yanava/mhd314/Documentation/Presentations/Live 08.pdf

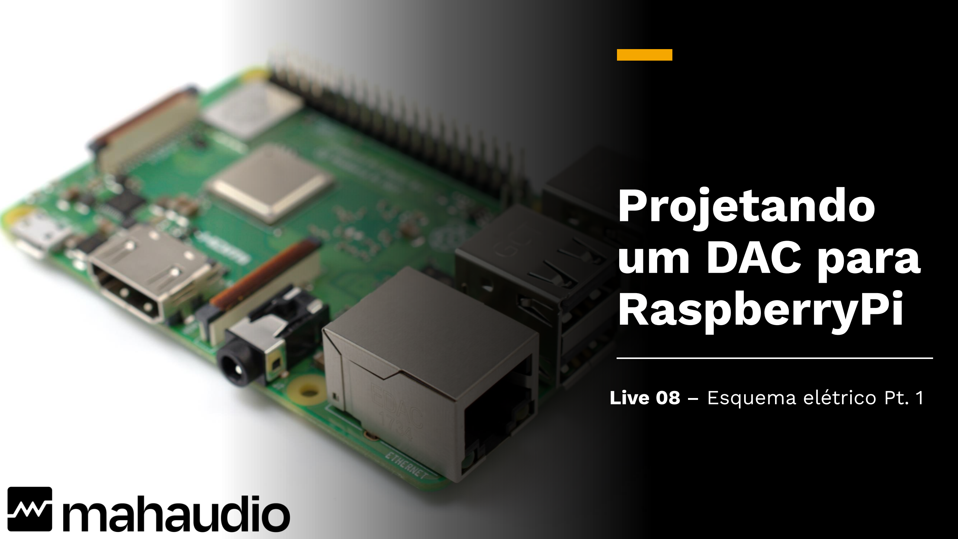
[picture p65: page 1]

# Projetando um DAC para RaspberryPi

## Live 08 – Esquema elétrico Pt. 1

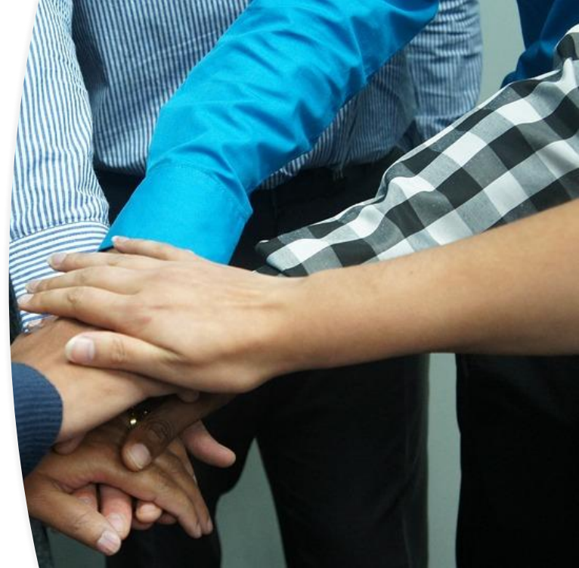
[picture p66: figure]

# Valeu apoiadores!

- Alexandre
- Beatriz
- Cássio
- Digão
- Edson
- Erik
- Henrique
- Leonardo B.
- Leonardo C.
- Luiz
- Rogério

# Resultados

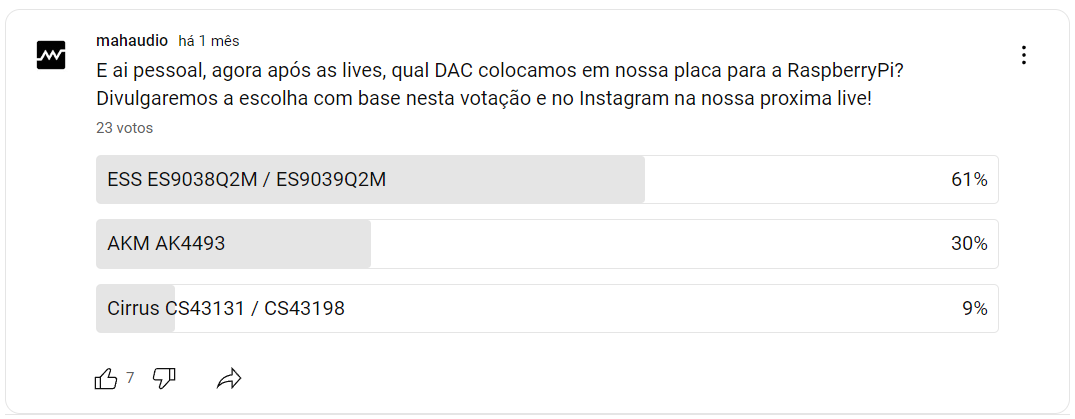
[picture p67: figure]

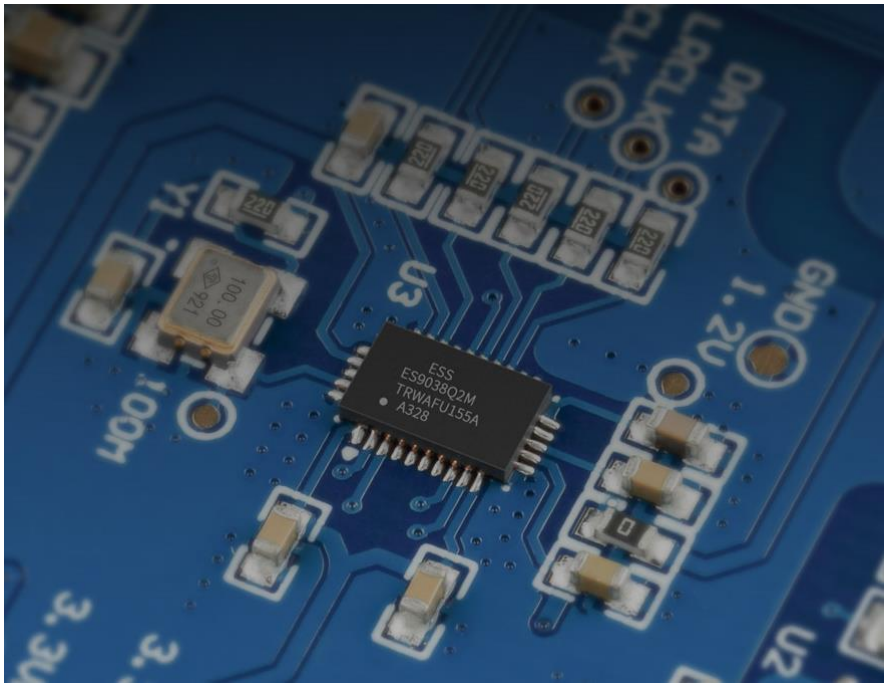
[picture p68: figure]

# Esquema elétrico com ES9038Q2M
