yanava/mhd314/Documentation/Presentations/Live 02.pdf

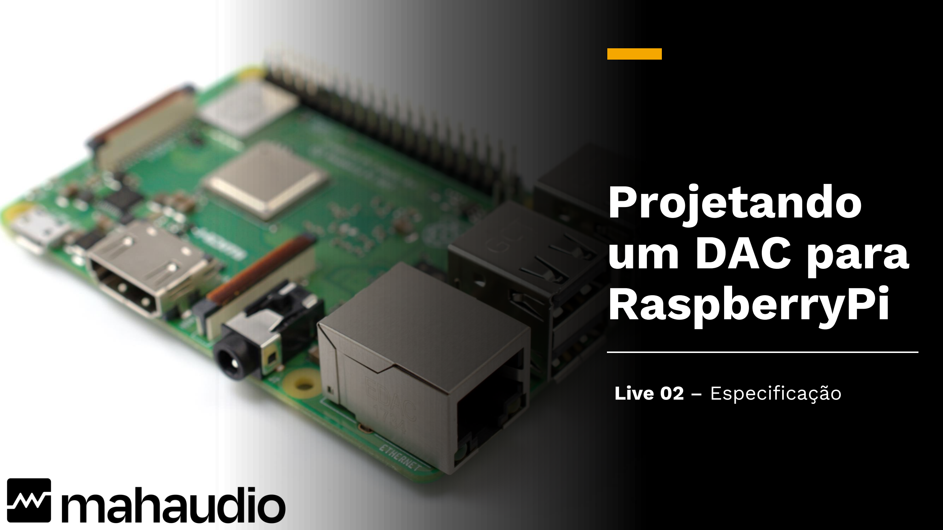
[picture p69: page 1]

# Projetando um DAC para RaspberryPi

## Live 02 – Especificação

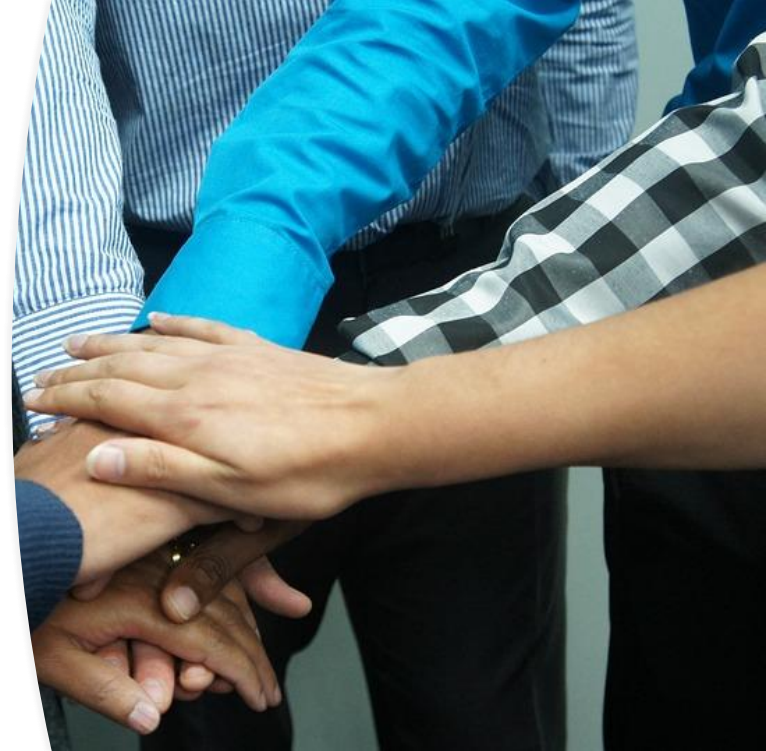
[picture p70: figure]

# Valeu apoiadores!

- Alexandre
- Beatriz
- Cássio
- Digão
- Edson
- Henrique
- Leonardo B.
- Leonardo C.
- Rogério

# Na live anterior

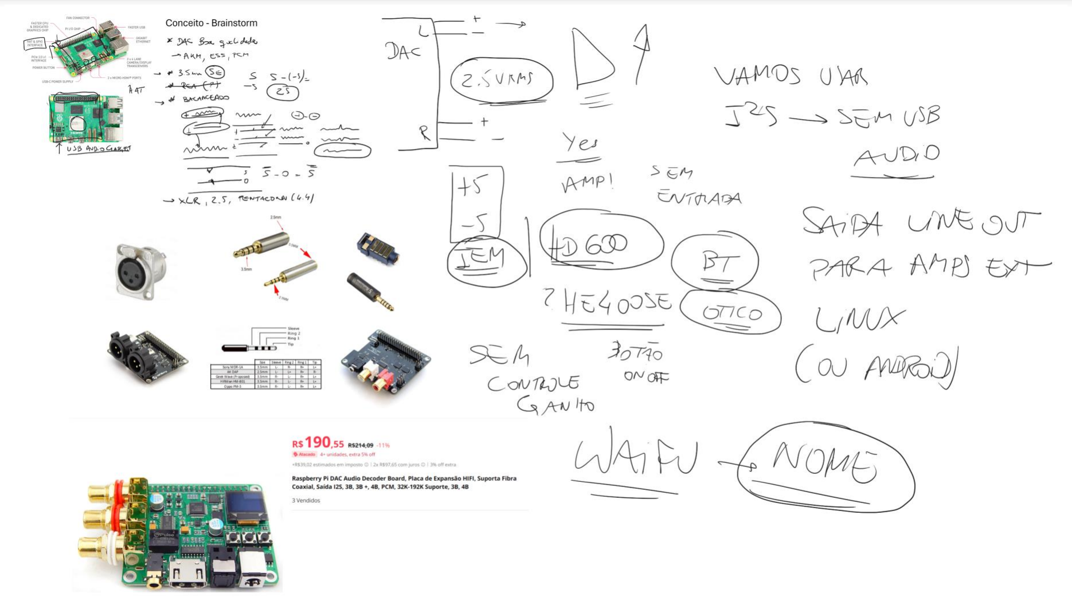
[picture p71: figure]

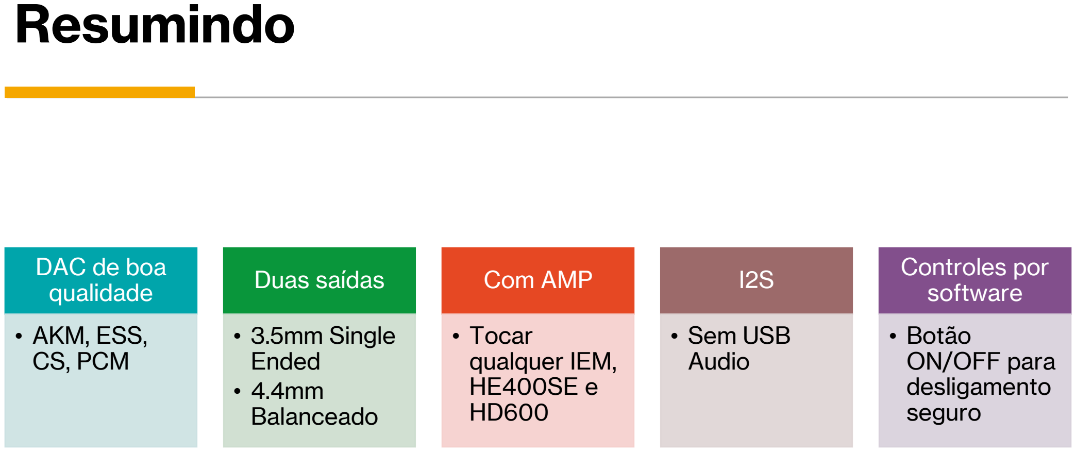
[picture p72: figure]
Resumindo; DAC de boa qualidade; • AKM, ESS, CS, PCM; Duas saídas; • 3.5mm Single Ended • 4.4mm Balanceado; Com AMP; • Tocar qualquer IEM, HE400SE e HD600; • Sem USB Audio; Controles por software; • Botão ON/OFF para desligamento seguro
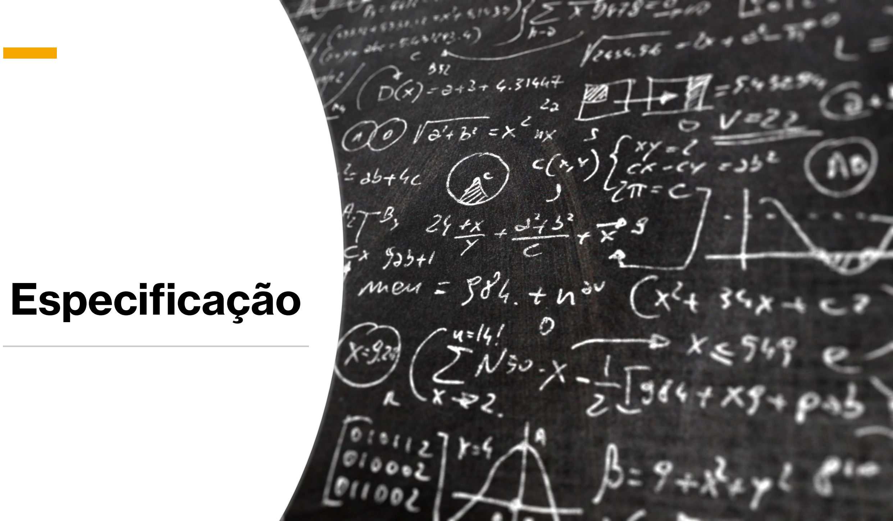
[picture p73: page 5]

# Especificação

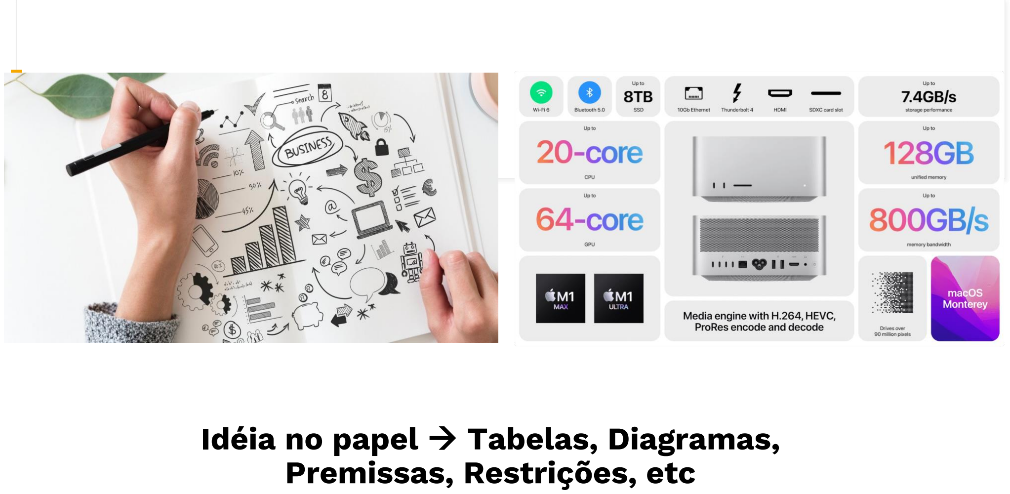
[picture p74: page 6]

Idéia no papel → Tabelas, Diagramas,

# Premissas, Restrições, etc

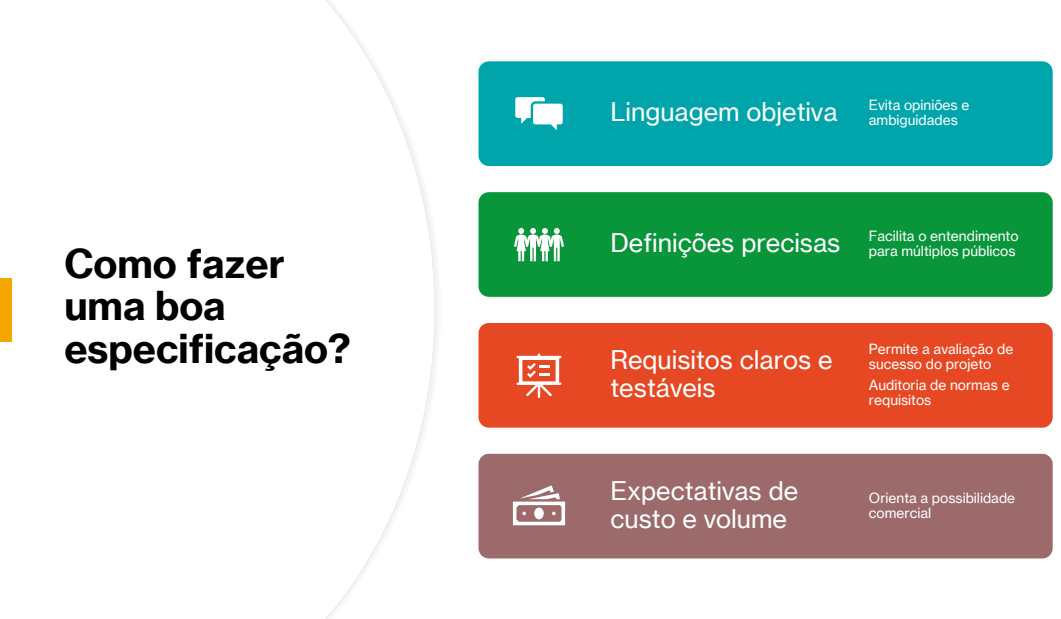
[picture p75: page 7]
Como fazer uma boa especificação?; Linguagem objetiva; Evita opiniões e; ambiguidades; Requisitos claros e testáveis; Expectativas de custo e volume; Orienta a possibilidade comercial

Definições precisas Facilita o entendimento

para múltiplos públicos

Permite a avaliação de
sucesso do projeto
Auditoria de normas e
requisitos

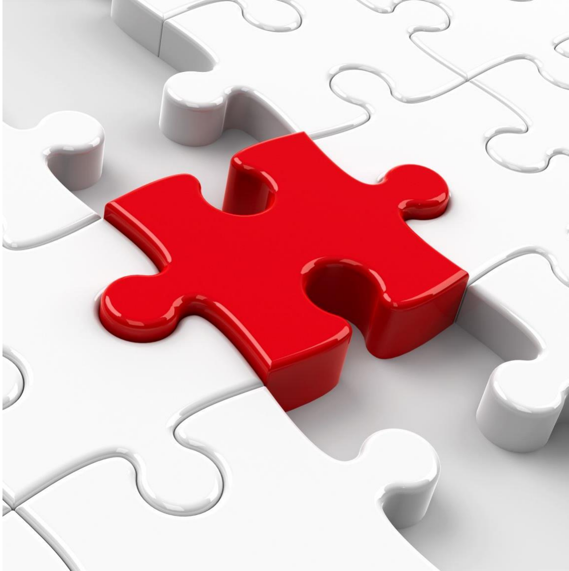
[picture p76: figure]

# Desafios

- Falta de informações
- Falta de conhecimento
- Dependência da escolha de componentes
- Sucesso (Volume) → desconhecido

# Modelo

Item | Descrição | Requisito | Prioridade | Justificativa
1 | Potência de Saída | 100mW SE / 200mW DIFF | Obrigatório | Fones exigentes
2 | Tamanho | 100 x 100 mm | Opcional | Caber no gabinete
3 | ... | ... | ... | ...

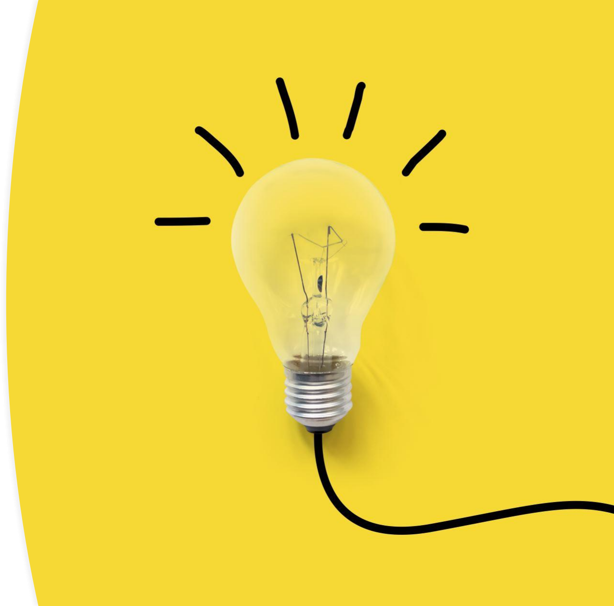
[picture p77: figure]

# Perguntas importantes

- Qual o tamanho físico?
- Quais são as entradas e seus requisitos?
- Quais são as saídas e seus requisitos?
- Quais são os requisitos de energia?
- Há normas a serem atendidas?
- Quais são os blocos do Sistema?
- Custo esperado?

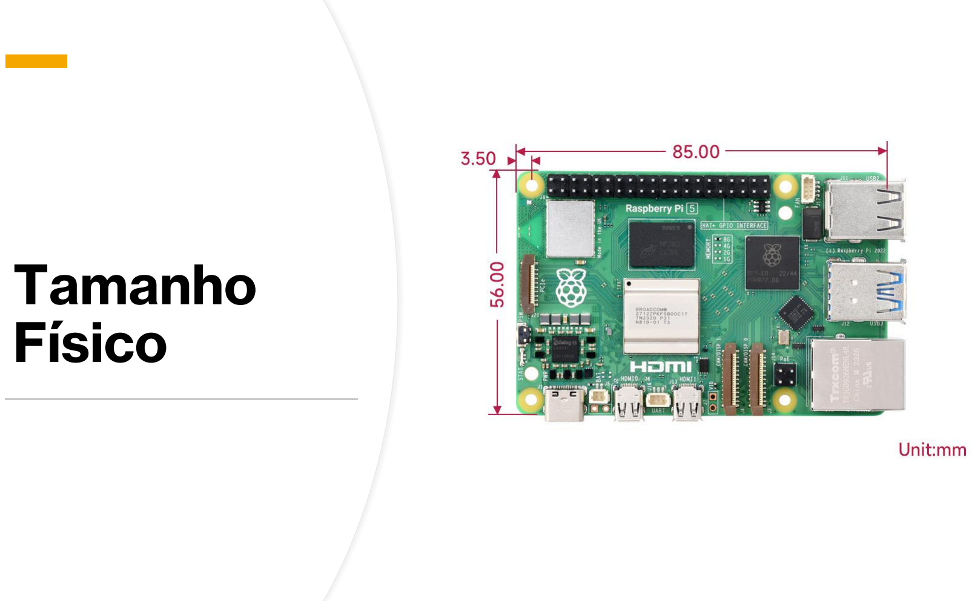
[picture p78: page 11]

# Tamanho Físico

# Alguns formatos em existência

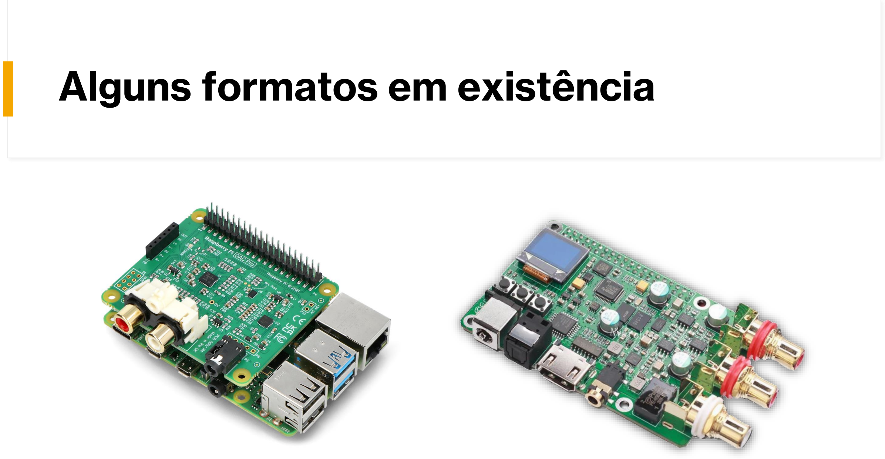
[picture p79: page 12]

# Padronização

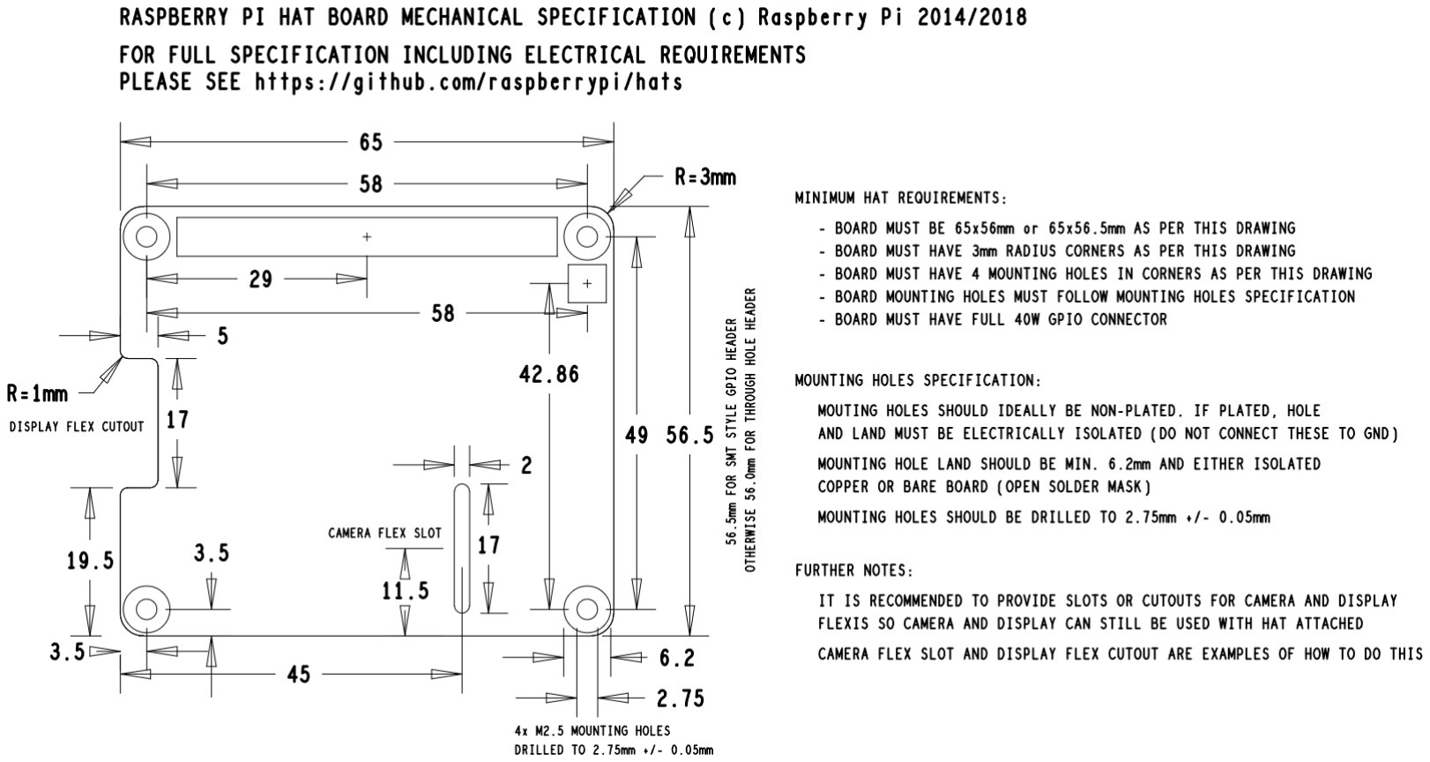
[picture p80: figure]
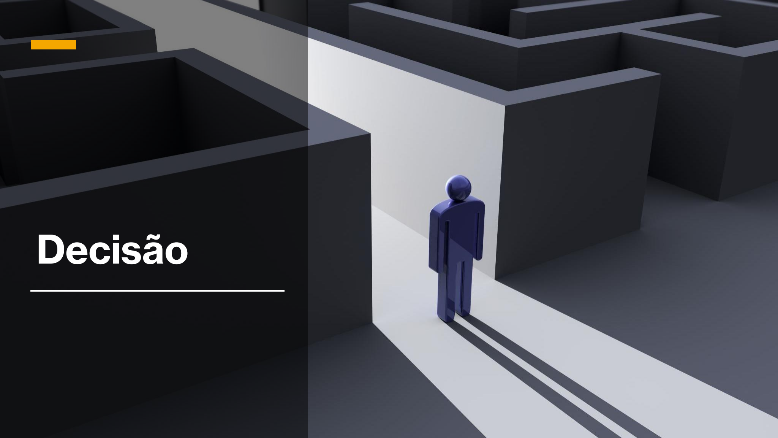
[picture p81: page 14]

# Decisão

# Entradas

## - Entrada de áudio → I2S

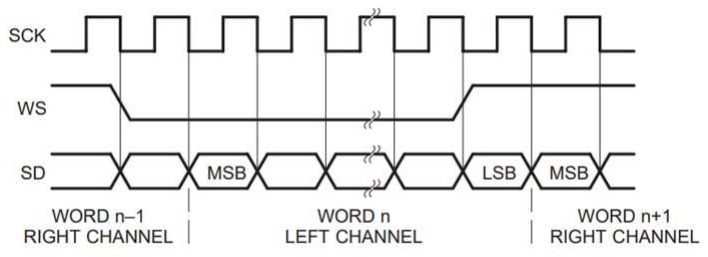
[picture p82: figure]
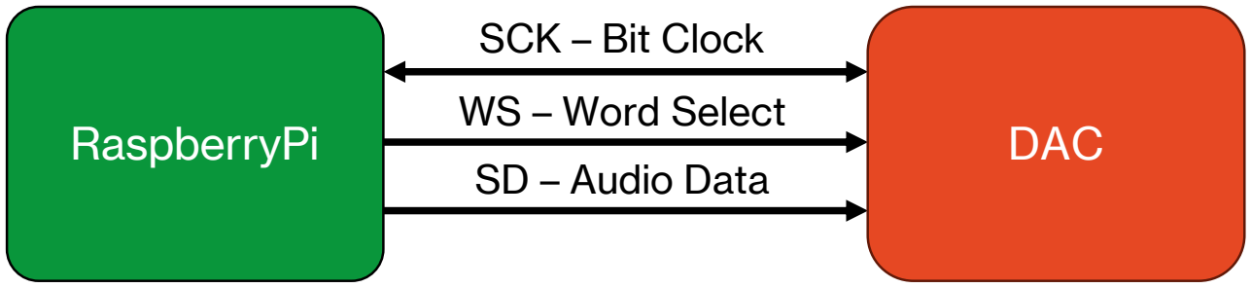
[picture p83: figure]
RaspberryPi; DAC; SD – Audio Data; SCK – Bit Clock; WS – Word Select

# Conector de expansão

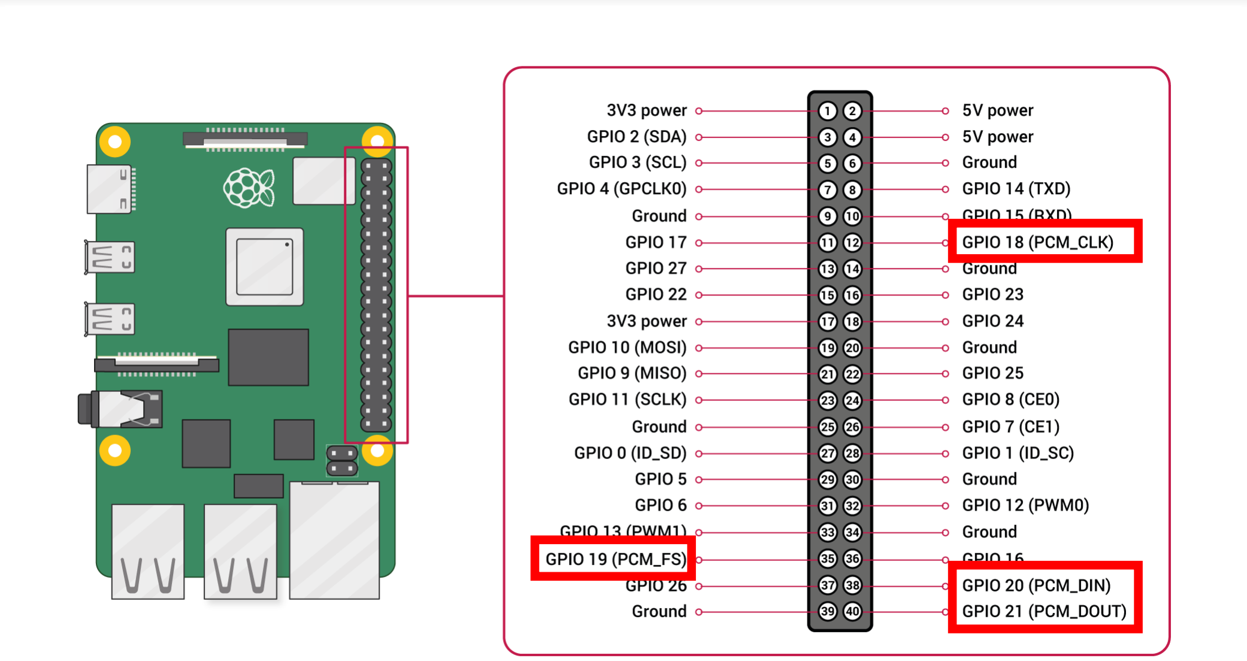
[picture p84: figure]

# Entradas

## - Entrada de configuração → Colocar o DAC no modo correto

- Depende do DAC → I2C, SPI ou similar
- Podemos deixar essa decisão para mais tarde?

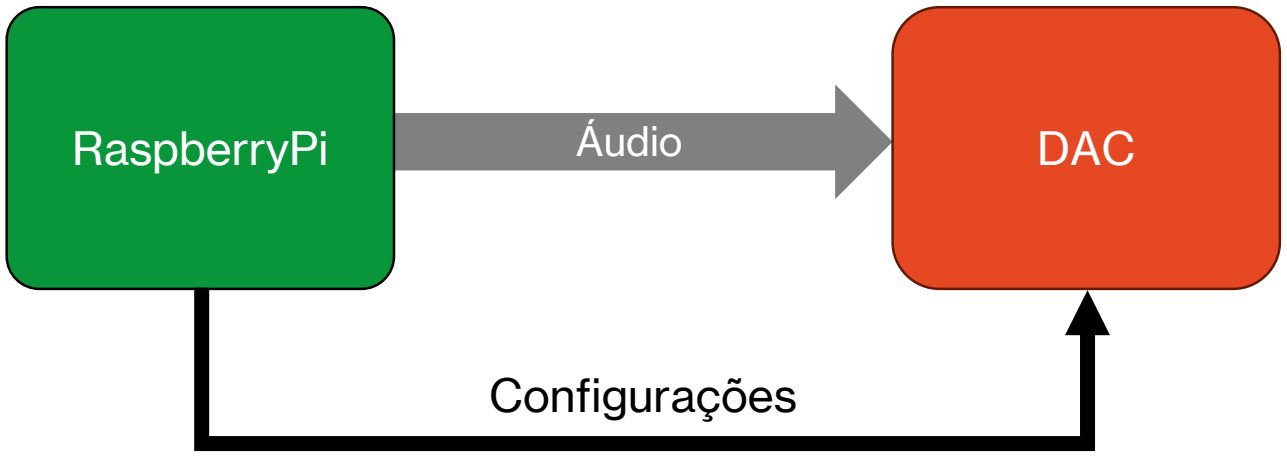
[picture p85: figure]
RaspberryPi; Áudio; DAC; Configurações

# Saídas

## - Já fizemos boa parte do trabalho no conceito inicial!

- Single Ended – 3.5mm
- Diferencial -4.4mm (Pentaconn)

## - Fones “guia”

- Qualquer IEM de referência → Qual?
- HD600
- HE400SE

## - Mas o que isto significa em termos de potência?

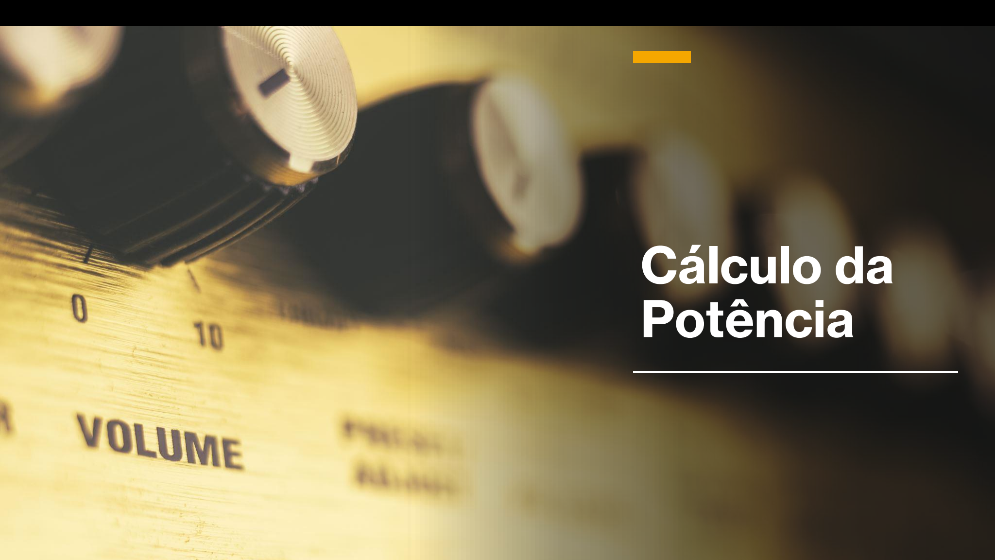
[picture p86: page 19]

# Cálculo da Potência

# Potência – Eletricidade vs Som

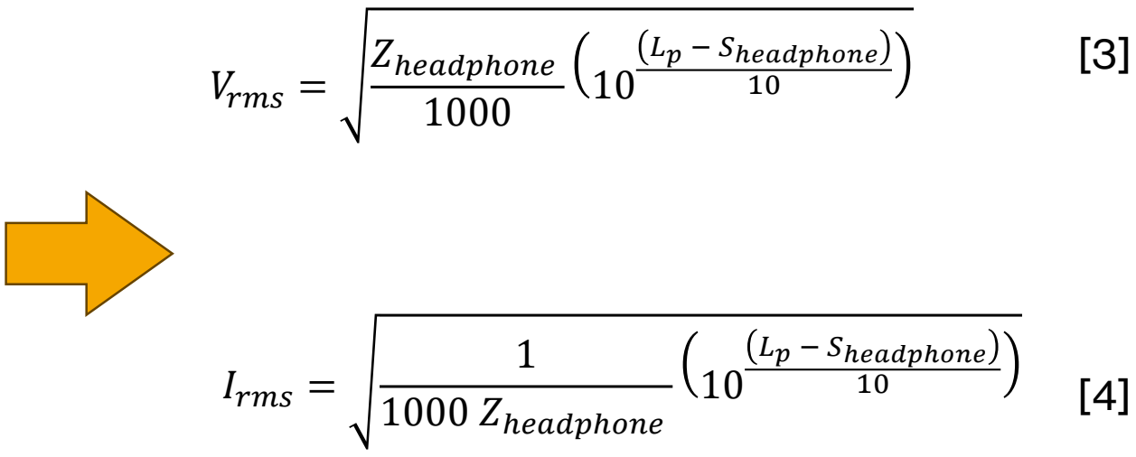
[picture p87: figure]
Vrms =; Zℎeadpℎone; Lp − Sℎeadpℎone 10; Irms =; 1000 Zℎeadpℎone; Lp − Sℎeadpℎone

P W =

Vrms

2

Zℎeadpℎone

= Zℎeadpℎone Irms

2

P(mW) = 10

Lp − Sℎeadpℎone
10

[1]

[2]

# Processo para especificar

## - Conhecer Sensibilidade (S) e Impedância (Z) para um fone alvo

## - Escolher nível de pressão sonora (Lp) adequado

## - Calcular potência (PRMS) e/ou tensão (VRMS) de saída

# Discussão – Pressão Sonora

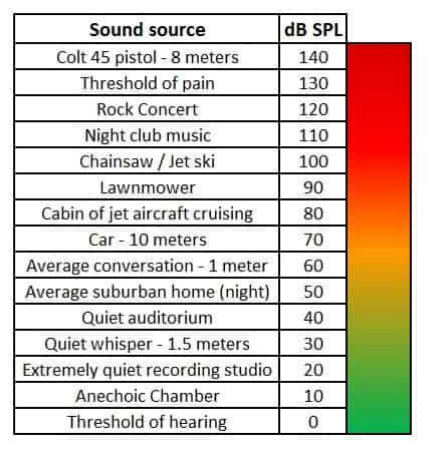
[picture p88: figure]

# Discussão – Nível de pressão sonora

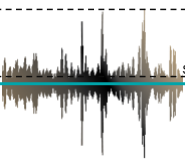
[picture p89: figure]

Som mais forte

Som mais fraco

Faixa dinâmica

Intensidade
Sonora

# Discussão – Nível de pressão sonora

Nivel operacional

Som mais forte

Som mais fraco
Piso de ruído

Limiar de Distorção

Relação sinal ruído
(SNR)

Headroom

Faixa dinâmica

# Nível operacional

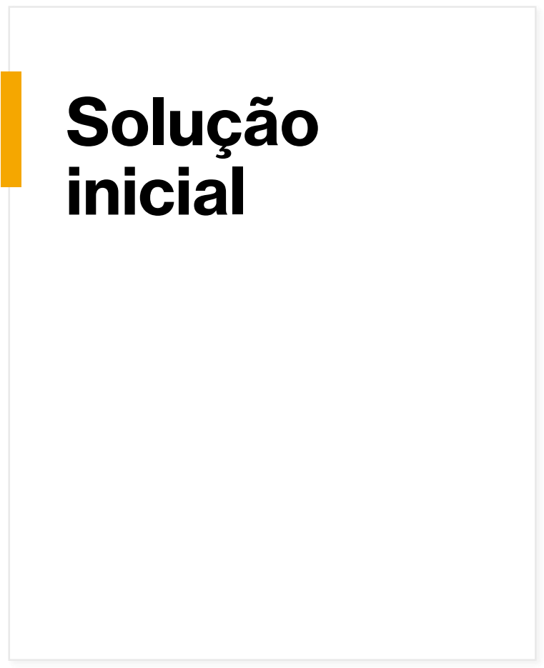
[picture p90: figure]
Solução inicial

# 90dBSPL

# Headroom 20dBSPL

# Pressão Sonora Max 110dBSPL

# Para os fones que decidimos

| Sennheiser HD600 | Hifiman HE400SE
Z | 322Ω | 25.3Ω
Lp | 110dBSPL
S | 100.5dB/mW | 88.7dB/mW
P | 8.91mW | 134.90mW
VRMS | 1.69V | 1.84V
IRMS | 5.27mA | 73.32mA

Fonte:
https://reference-audio-analyzer.pro/en/report/hp/sennheiser-hd-600.phphttps://reference-audio-analyzer.pro/en/report/hp/hifiman-he400se-v2.php

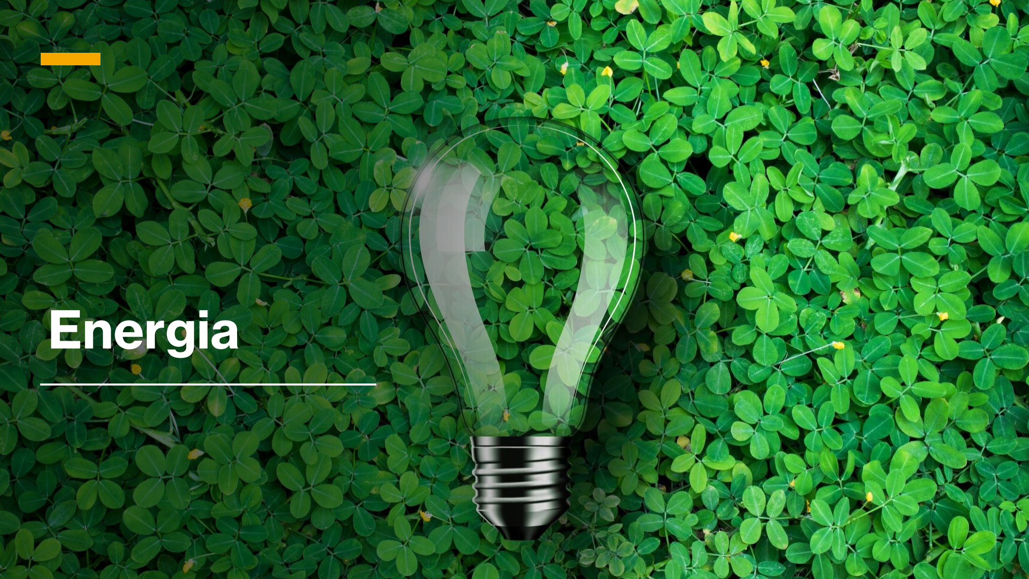
[picture p91: page 27]

# Energia

# Entrada de energia

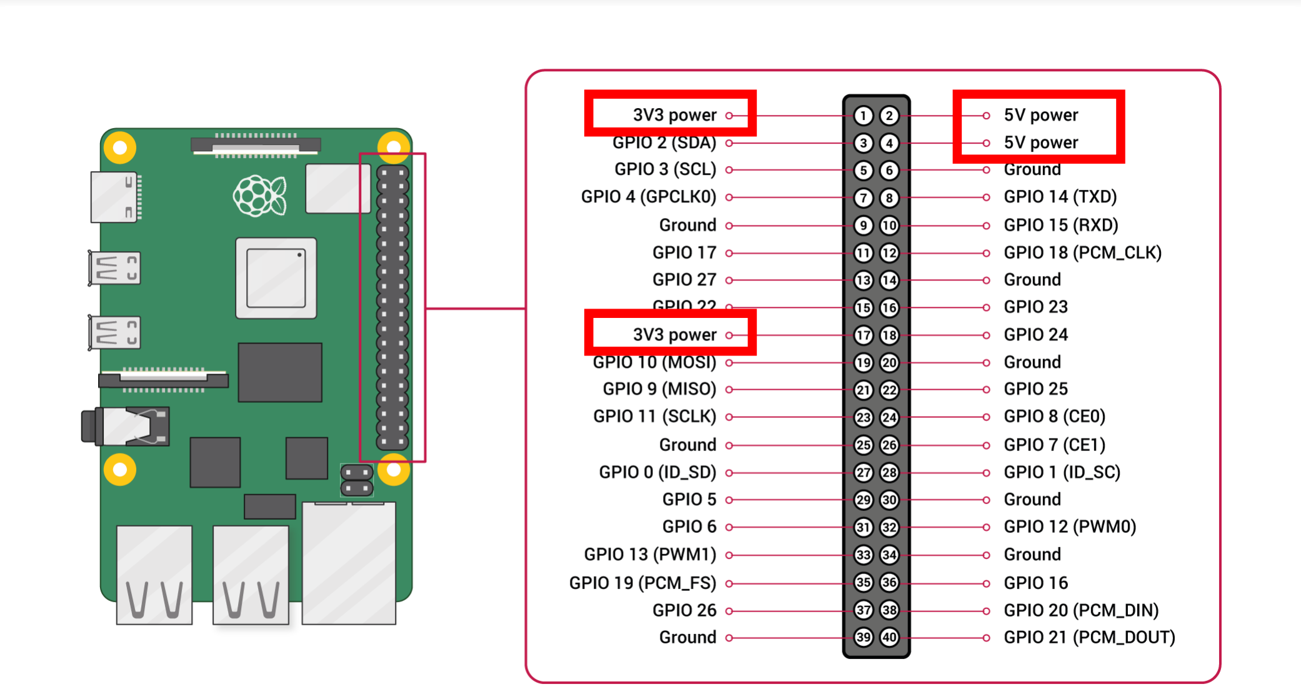
[picture p92: figure]

# Entrada de Energia

## - Duas tensões de entrada

- 5V – Tudo que tem a ver com o DAC
- 3.3V – Tensão de níveis lógicos

## - Potência necessária → Vai depender dos componentes

- Não ultrapassar um máximo pode ser um bom guia
- 5V – 500mA (2.5W)
- 3.3V – 500mA (1.65W)

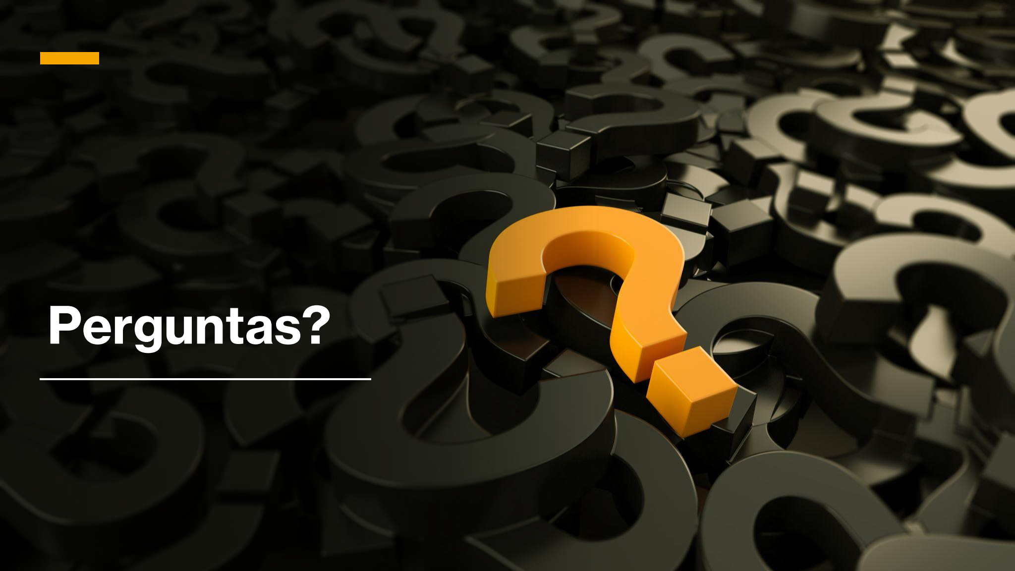
[picture p93: page 30]

# Perguntas?

# Próxima Live

## - Partimos da tabela de spec

## - Vamos desenhar o diagrama de blocos!
