yanava/mhd314/Documentation/Presentations/Live 04.pdf

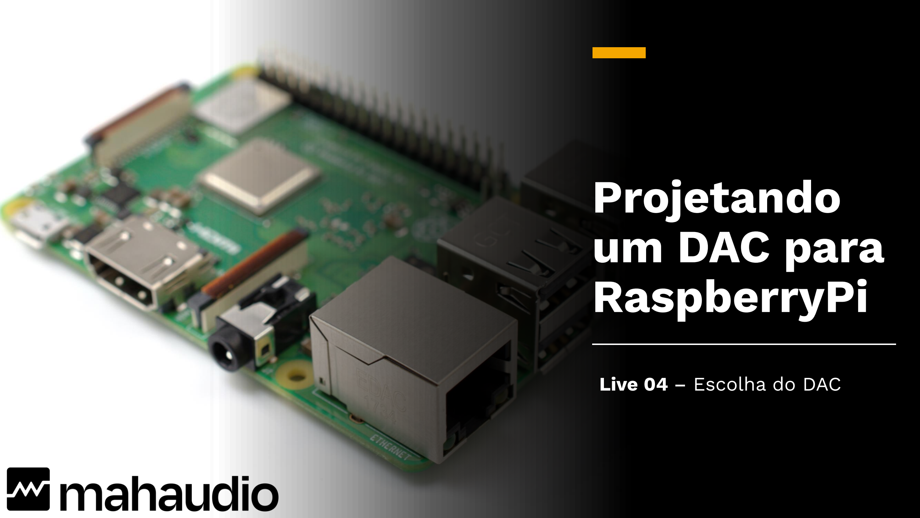
[picture p99: page 1]

# Projetando um DAC para RaspberryPi

Live 04 – Escolha do DAC


## Valeu apoiadores!

- Alexandre
- Beatriz
- Cássio
- Digão
- Edson
- Henrique
- Leonardo B.
- Leonardo C.
- Rogério

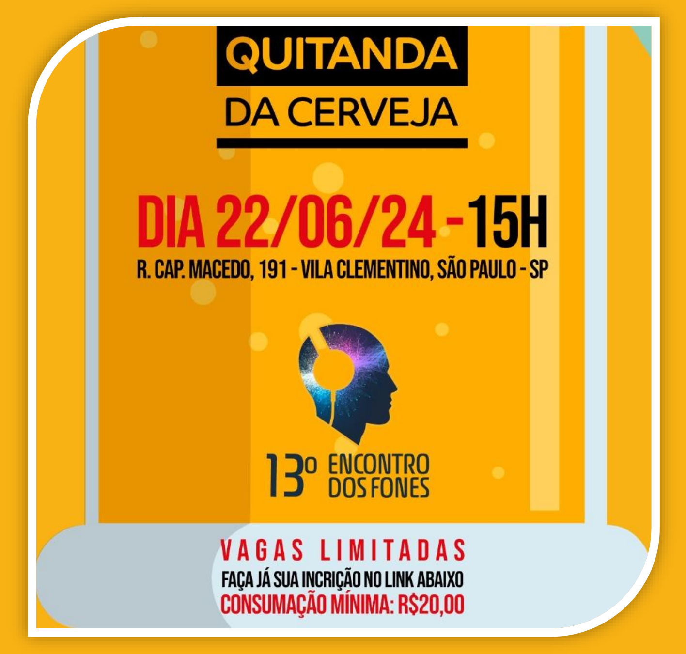
[picture p100: figure]

# Na live anterior

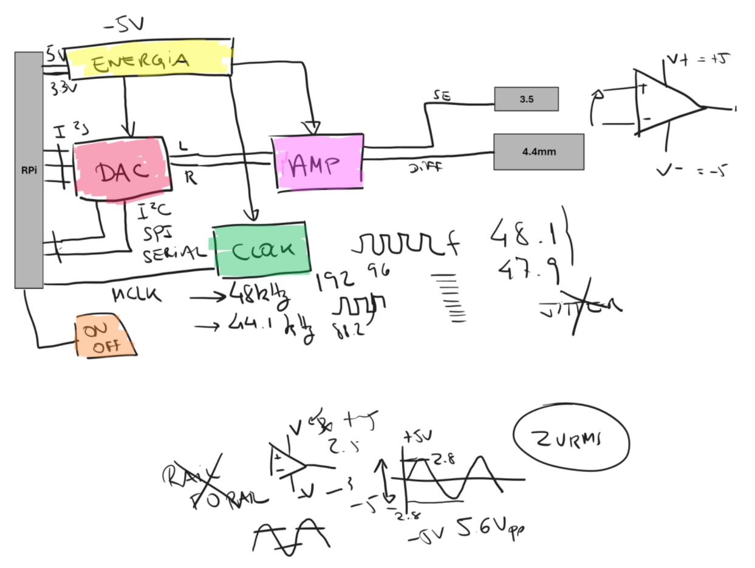
[picture p101: figure]

## Resumindo

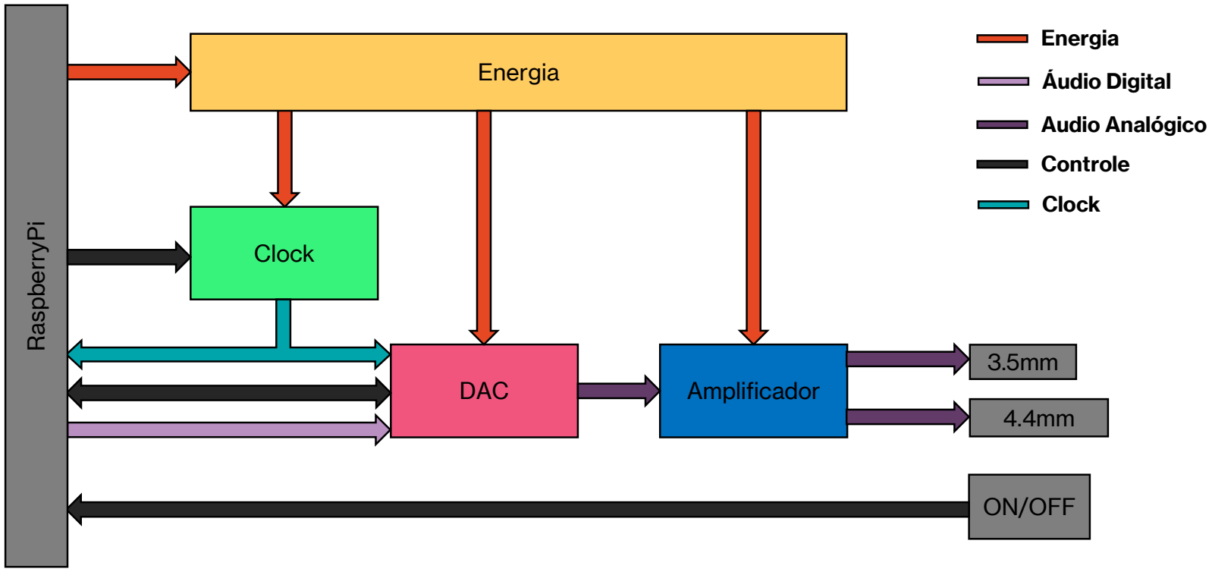
[picture p102: figure]
Energia; DAC; Amplificador; Clock; ON/OFF; RaspberryPi; Audio Analógico; Controle; Áudio Digital
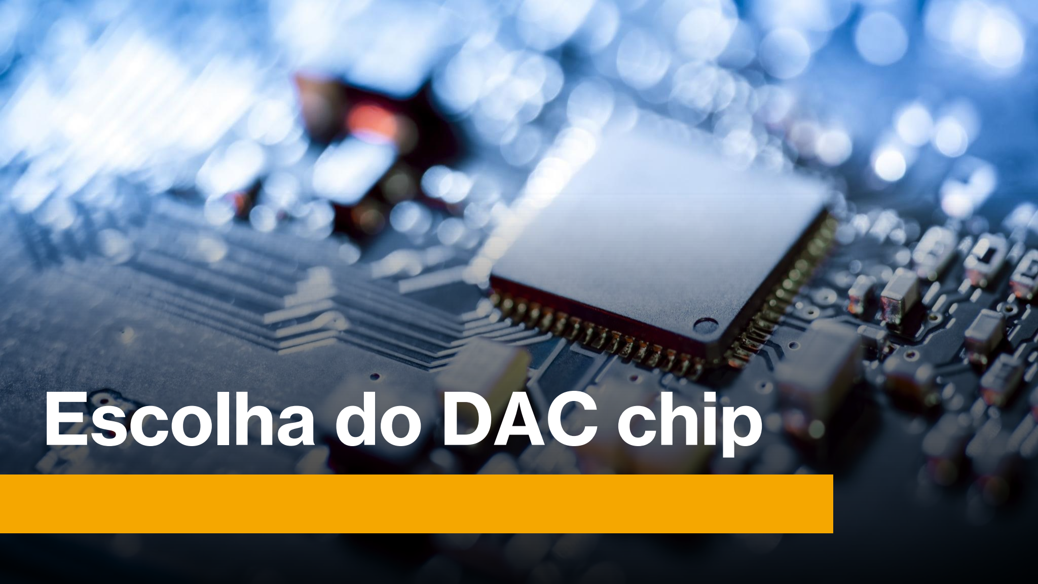
[picture p103: page 6]

# Escolha do DAC chip

## Função de um DAC

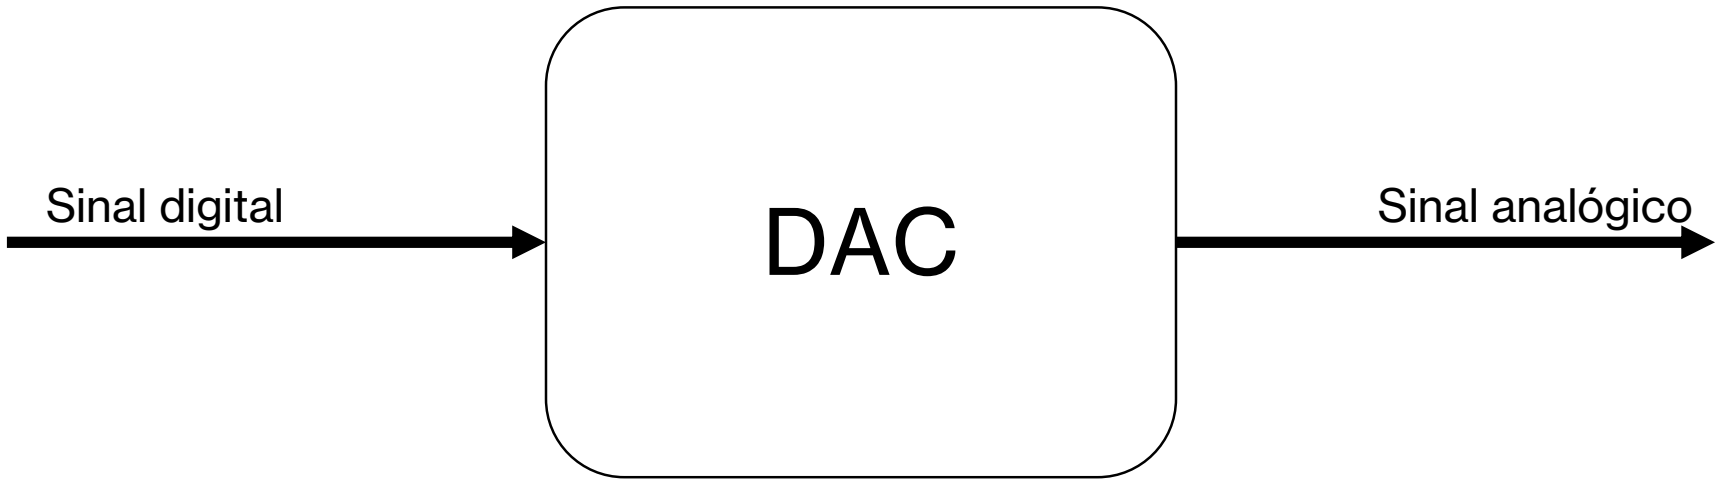
[picture p104: figure]
DAC Sinal digital; Sinal analógico

## Tipos de DAC

- Resistivo
- Escada R-2R
- Delta-Sigma

## Resistivo

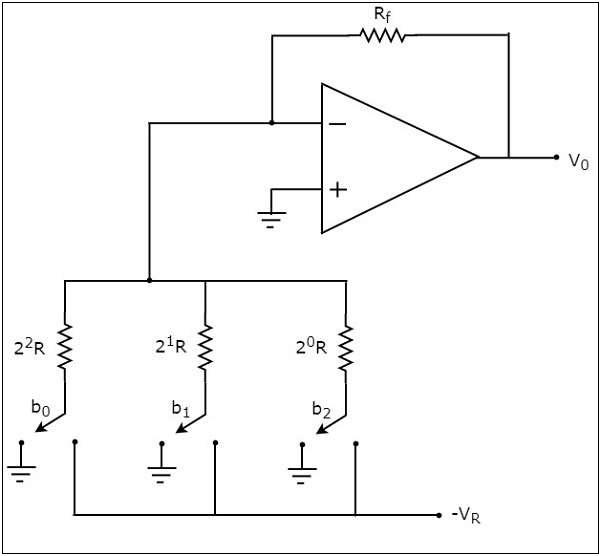
[picture p105: figure]

R-2R

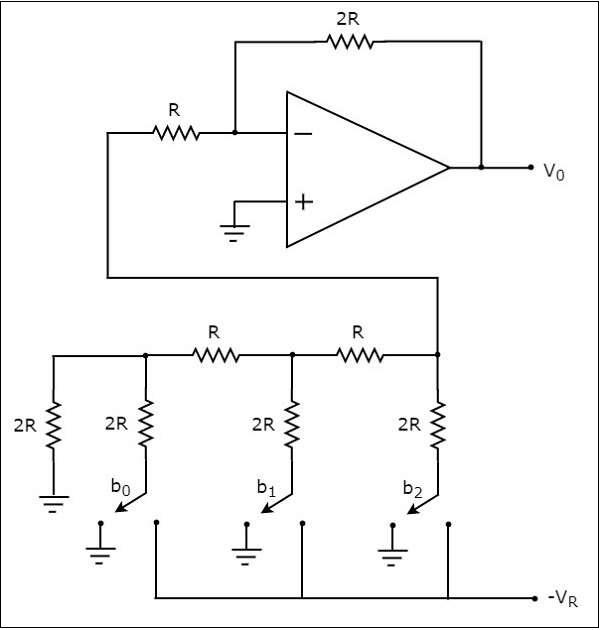
[picture p106: figure]

## Delta-Sigma

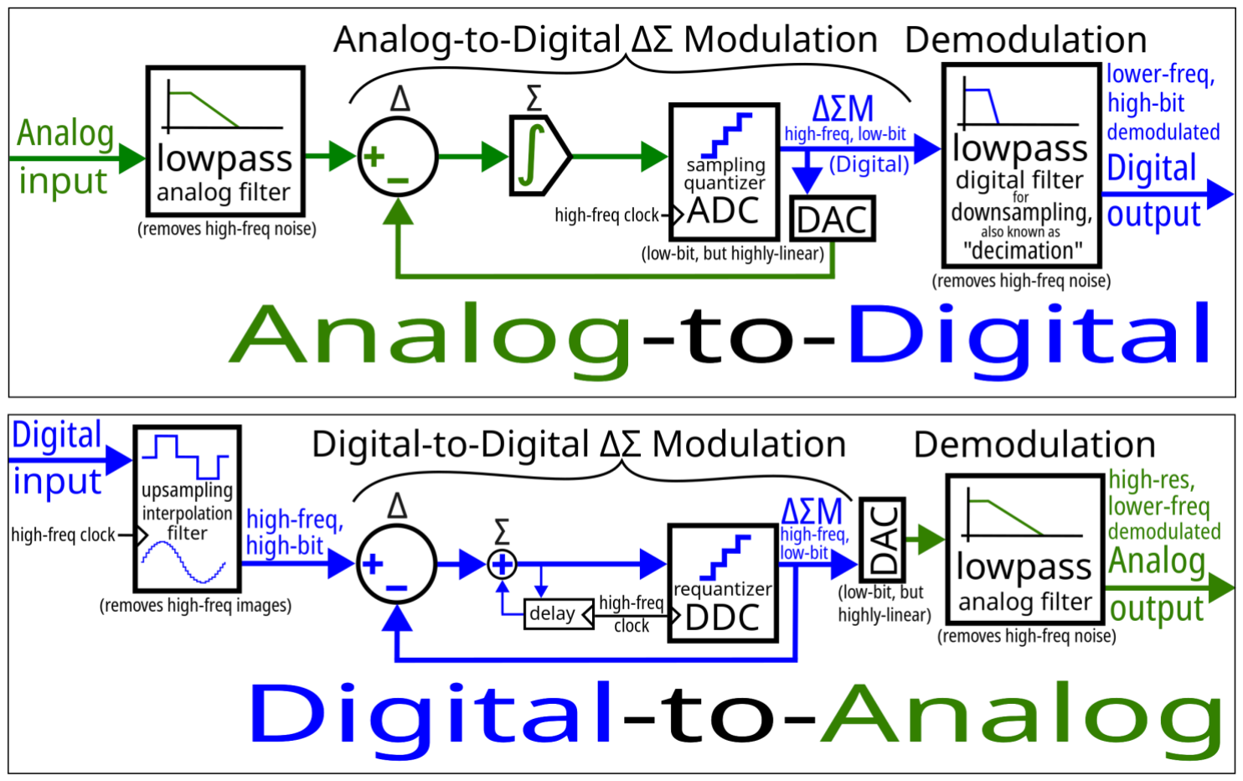
[picture p107: figure]

## Por que Delta-Sigma?

- Popular no mercado
- Alta linearidade → Baixa distorção
- Sobreamostragem → Baixo ruído
- Filtros externos facilmente implementados

Podemos falar mais sobre numa próxima live!

## Alguns pontos esquecidos

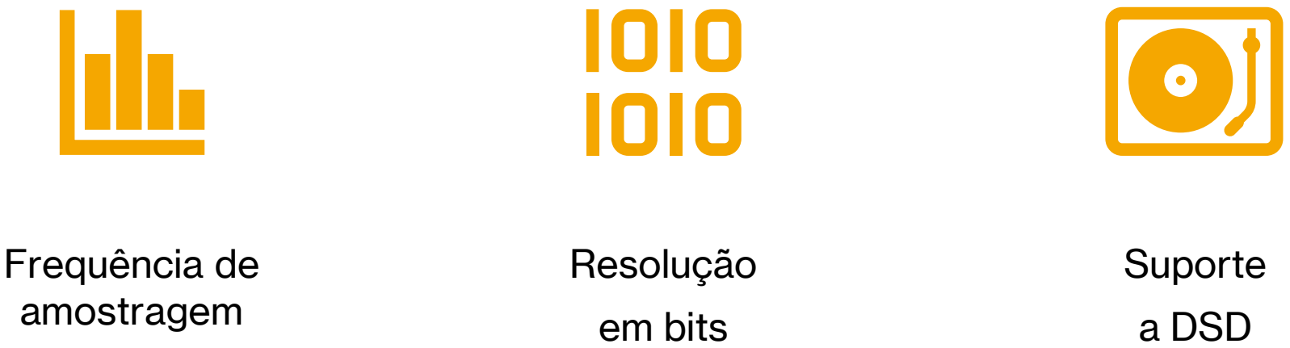
[picture p108: figure]
Frequência de amostragem; Resolução; em bits; Suporte; a DSD

## Outras características técnicas importantes

- SNR
- THD+N
- Faixa dinâmica
- Tipo da saída (diferencial / single-ended)
- Consumo de energia
- Tamanho / Encapsulamento

## Características não técnicas

- Preço unitário
- Disponibilidade
- Data de lançamento
- Popularidade
- Reputação do fabricante

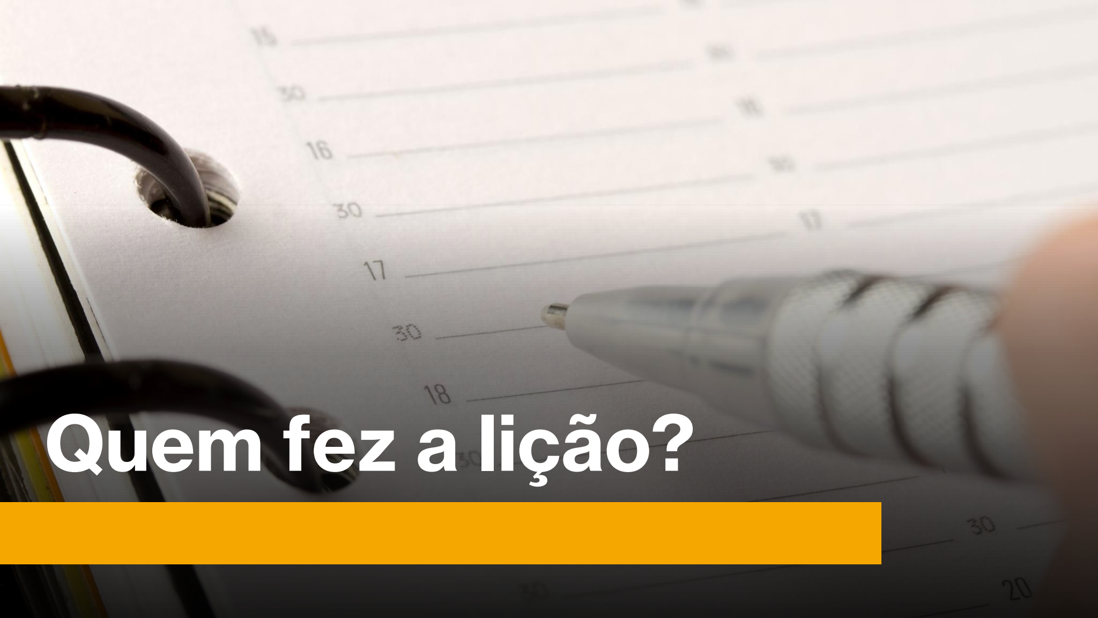
[picture p109: page 16]

# Quem fez a lição?

## Marcas candidatas

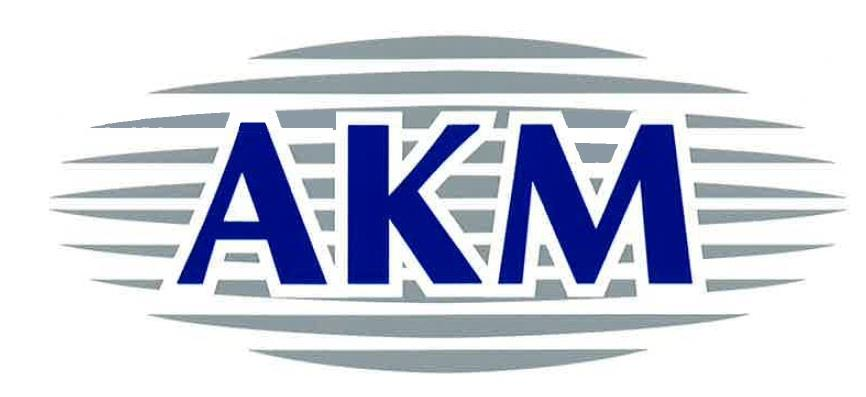
[picture p110: figure]
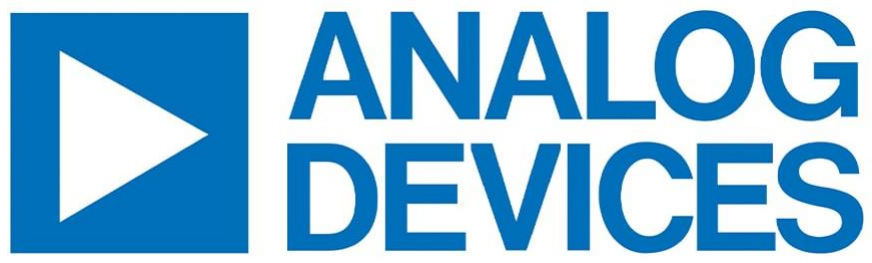
[picture p111: figure]
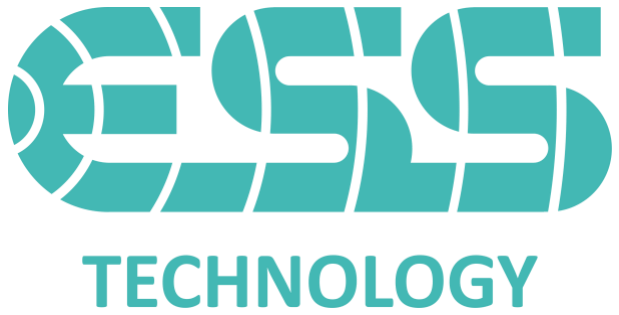
[picture p112: figure]
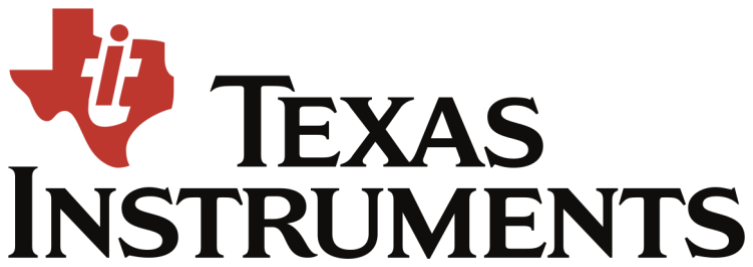
[picture p113: figure]
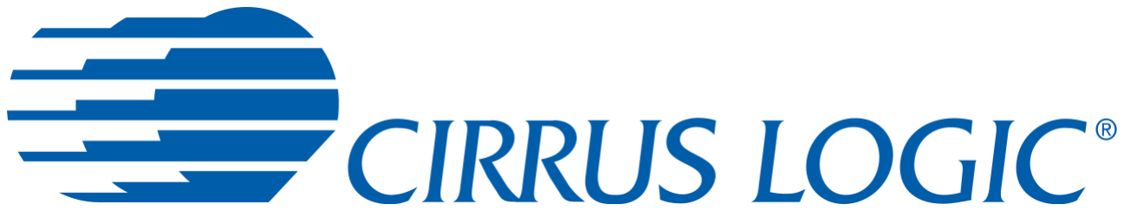
[picture p114: figure]
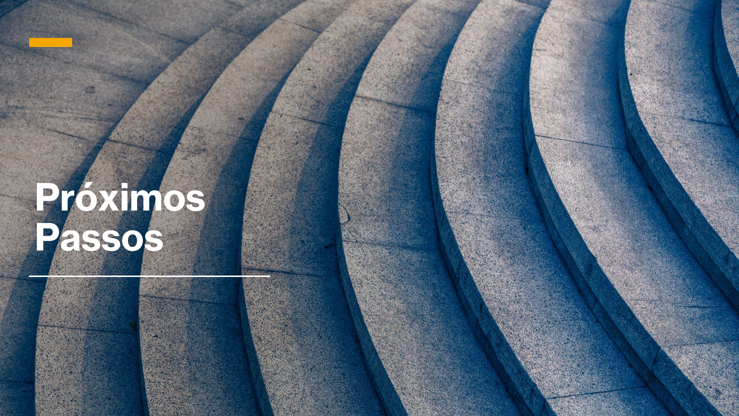
[picture p115: page 18]

# Próximos Passos
