yanava/mhd314/Documentation/Presentations/Live 05.pdf

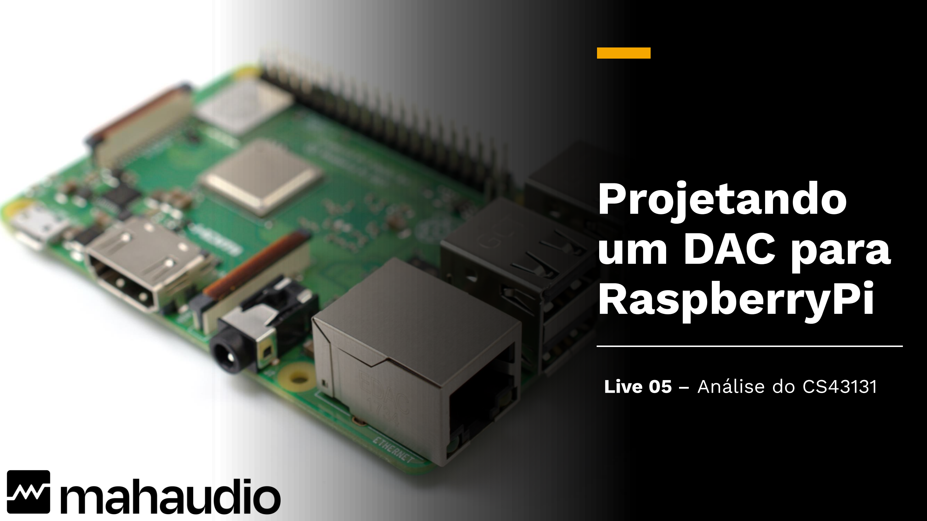
[picture p125: page 1]

# Projetando um DAC para RaspberryPi

## Live 05 – Análise do CS43131


# Valeu apoiadores!

- Alexandre
- Beatriz
- Cássio
- Digão
- Edson
- Erik
- Henrique
- Leonardo B.
- Leonardo C.
- Rogério

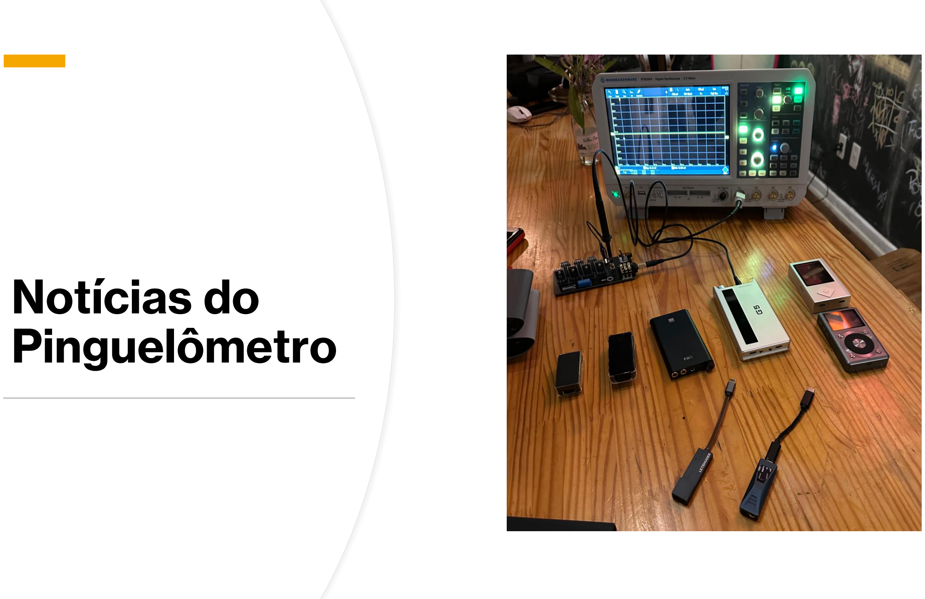
[picture p126: page 3]

# Notícias do Pinguelômetro

# Na live anterior

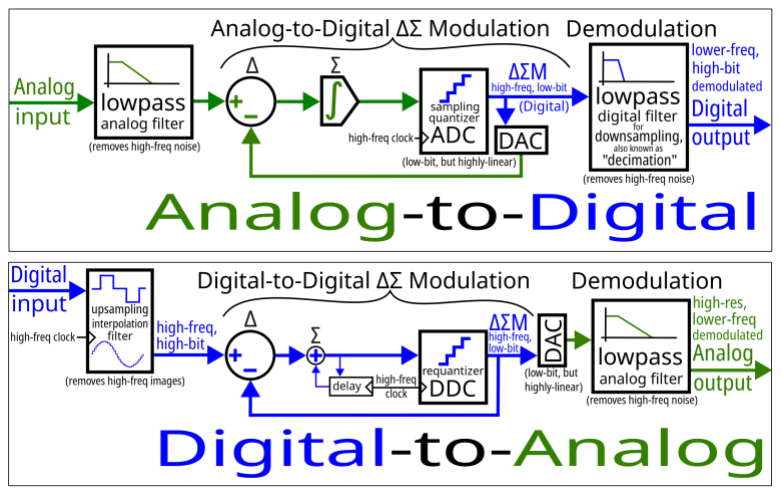
[picture p127: figure]
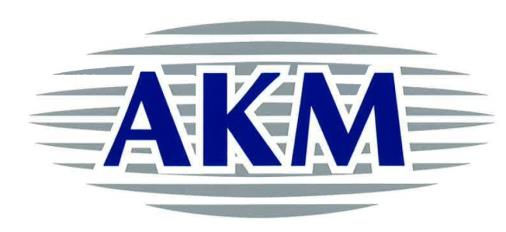
[picture p128: figure]
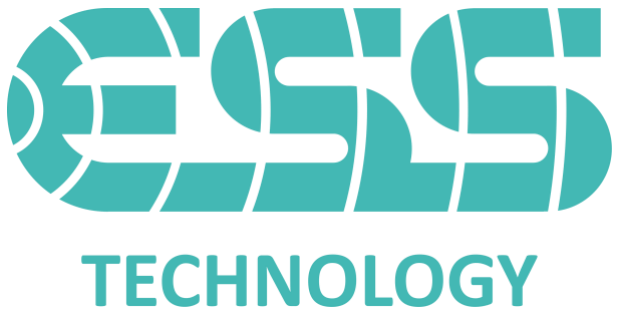
[picture p129: figure]

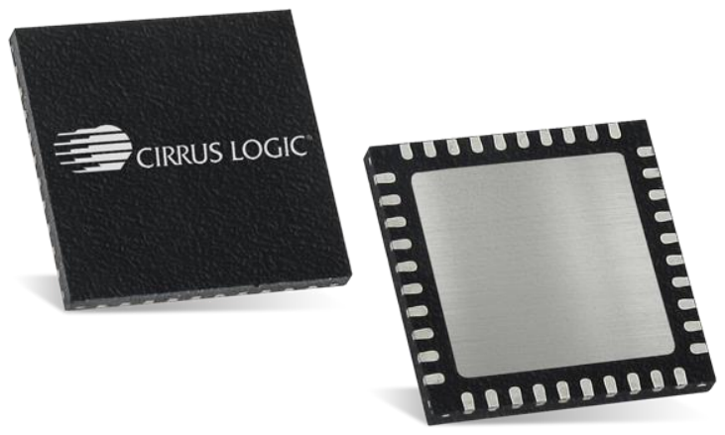
[picture p130: figure]

# Análise do

CS43131


# Próximos Passos
