yanava/mhd314/Documentation/Presentations/Live 06.pdf

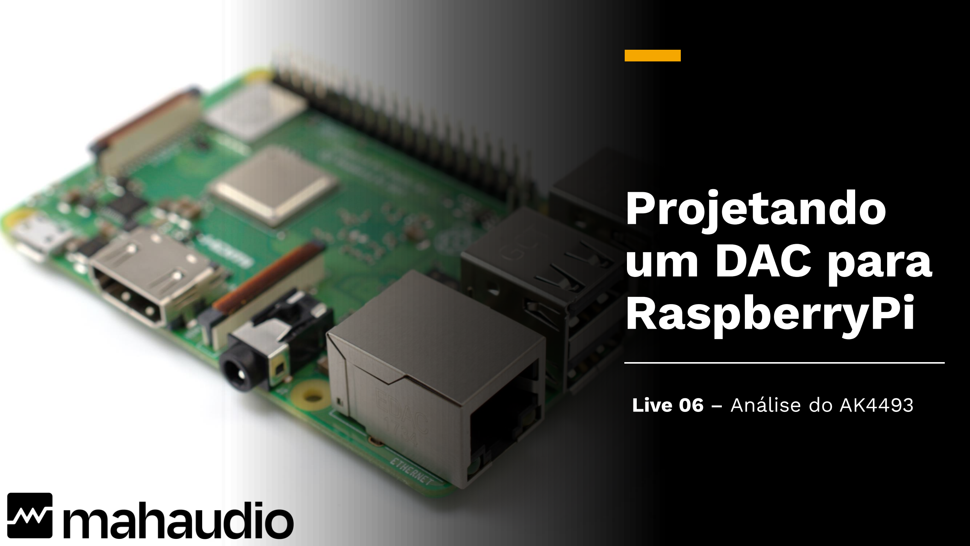
[picture p131: page 1]

# Projetando um DAC para RaspberryPi

## Live 06 – Análise do AK4493


# Valeu apoiadores!

- Alexandre
- Beatriz
- Cássio
- Digão
- Edson
- Erik
- Henrique
- Leonardo B.
- Leonardo C.
- Rogério

# Na live anterior

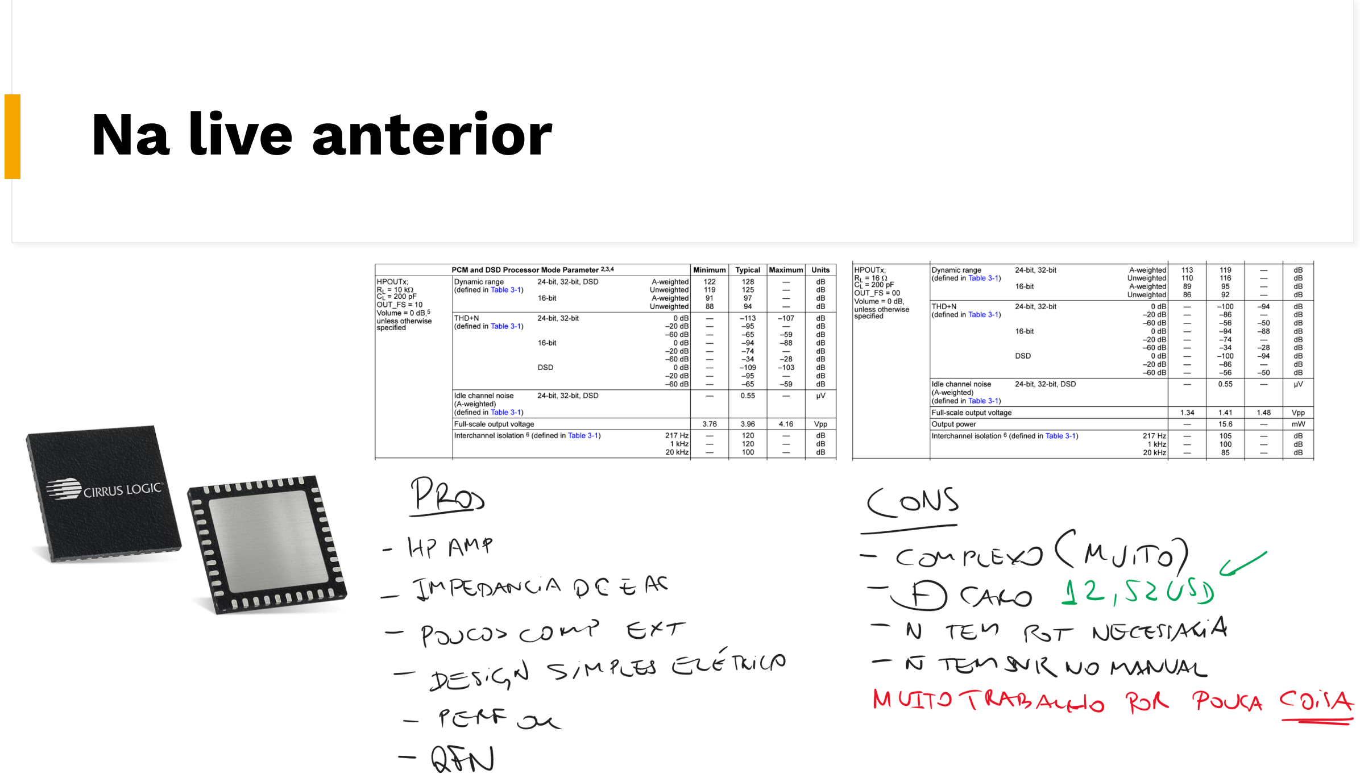
[picture p132: page 3]

# Dynamic Range vs SNR

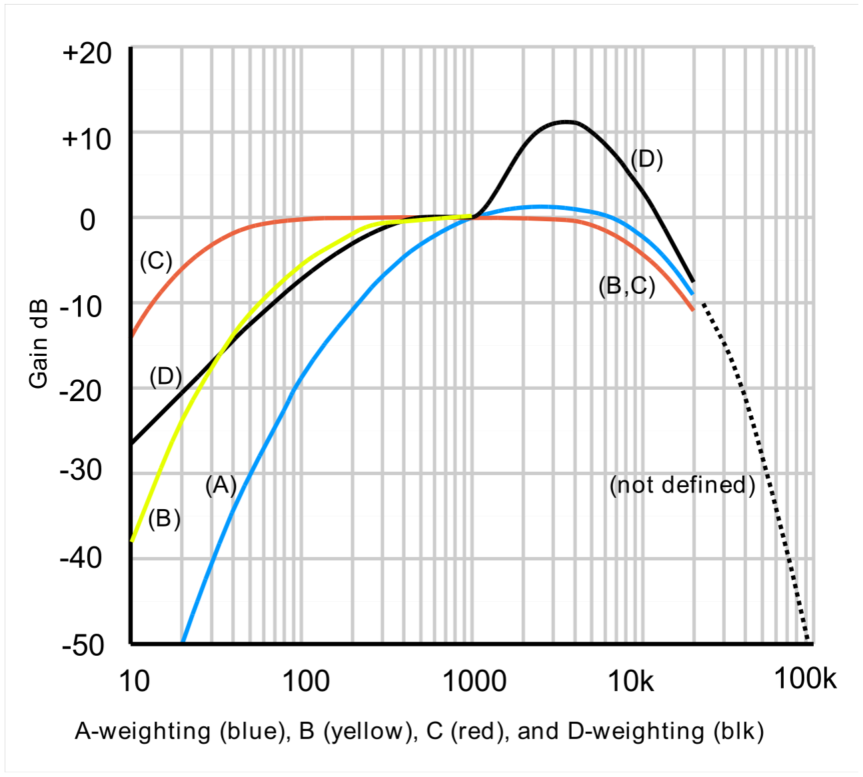
[picture p133: figure]

# A-weight

- Calibração para percepção humana
- Curvas padrão → Instrumento calibra

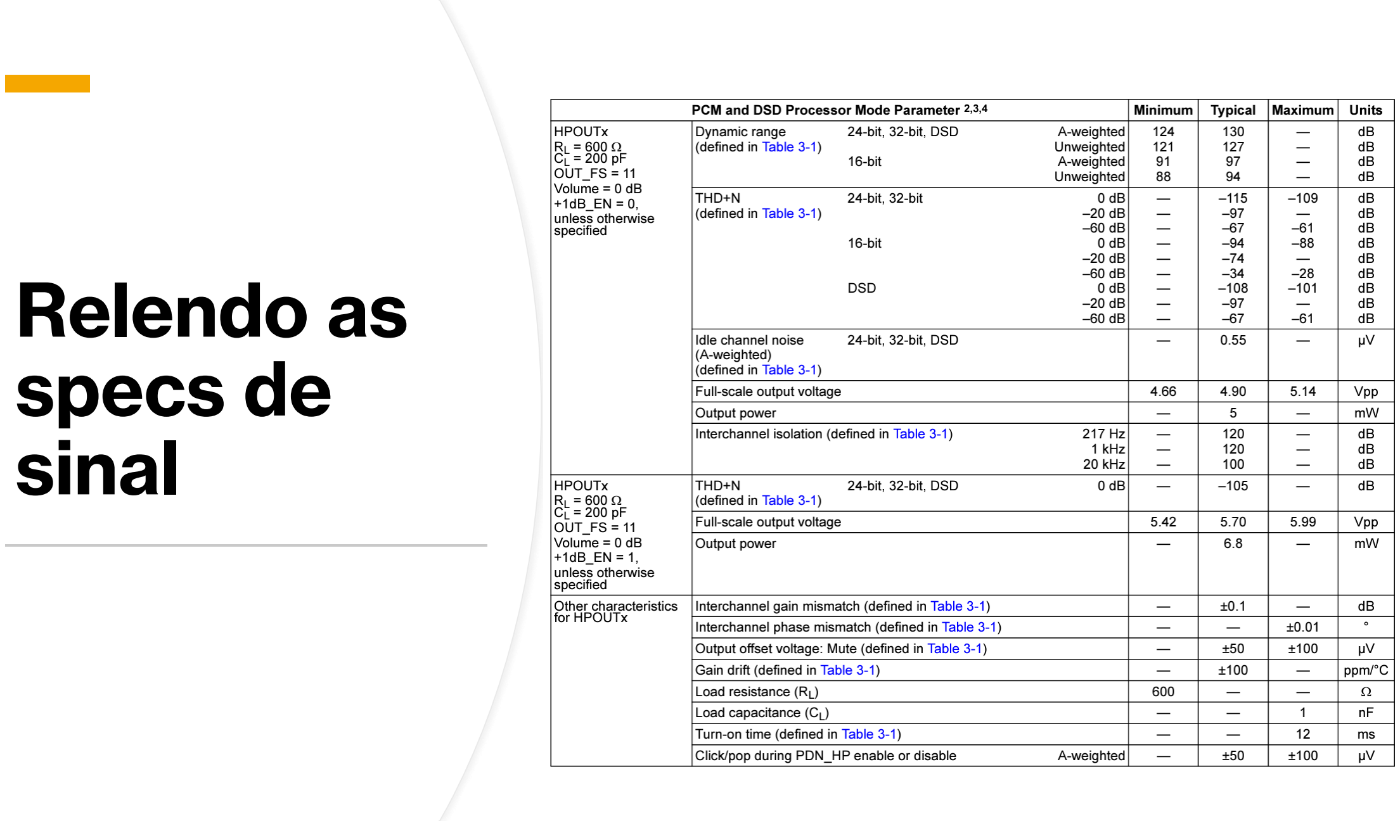
[picture p134: page 6]

# Relendo as specs de sinal

# Um resumo

Pros

SNR = 130dB

THD+N = -115dB

Amplificador de Fones

Medição de impedância

PLL interno

Poucos componentes externos

Cons

Complexo

Caro – USD 12.52

Fraco - 30mW em 32ohms (SE)

Saída pseudo diferencial

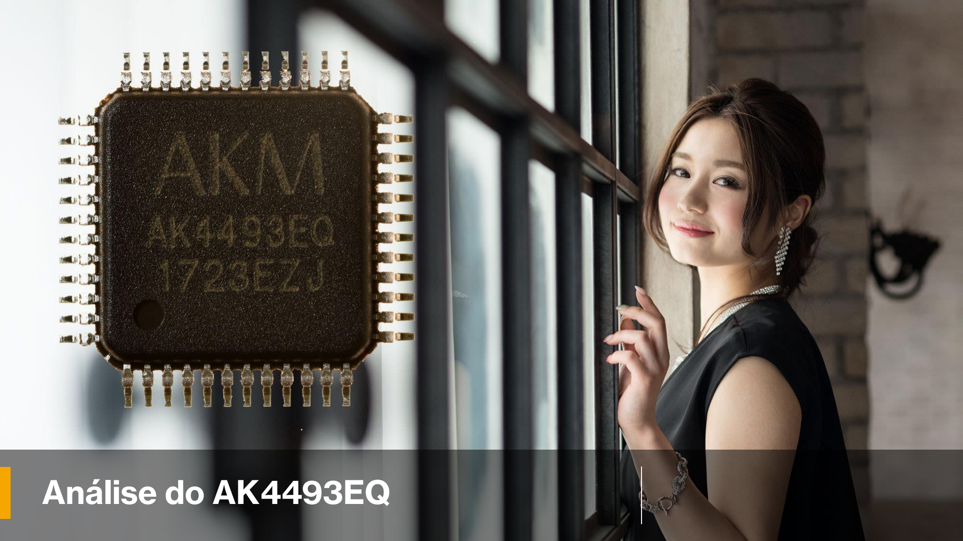
[picture p135: page 8]

# Análise do AK4493EQ


# Próximos Passos
