yanava/mhd314/Documentation/Presentations/Live 07.pdf

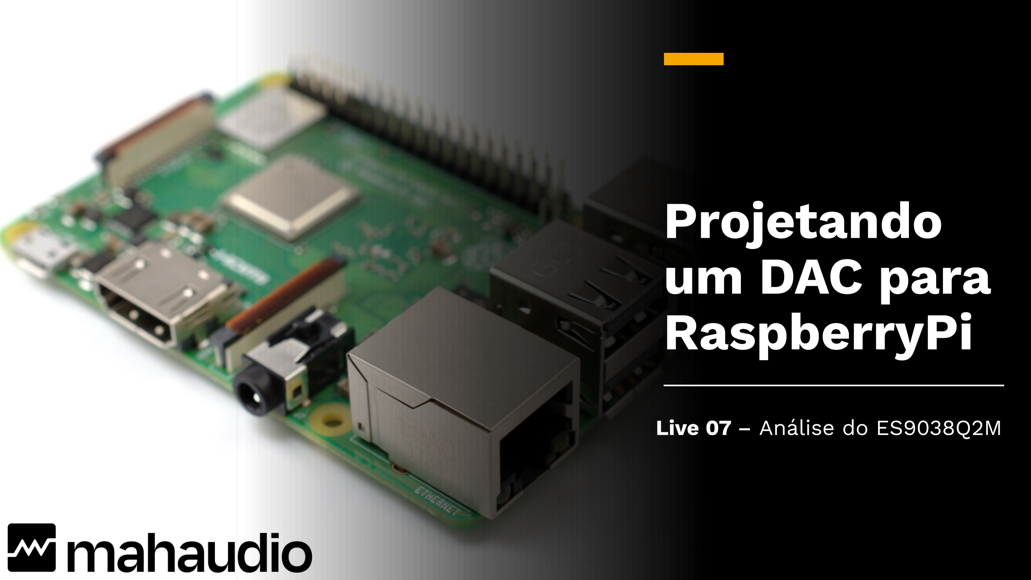
[picture p136: page 1]

# Projetando um DAC para RaspberryPi

## Live 07 – Análise do ES9038Q2M


# Valeu apoiadores!

- Alexandre
- Beatriz
- Cássio
- Digão
- Edson
- Erik
- Henrique
- Leonardo B.
- Leonardo C.
- Rogério

# Na live anterior

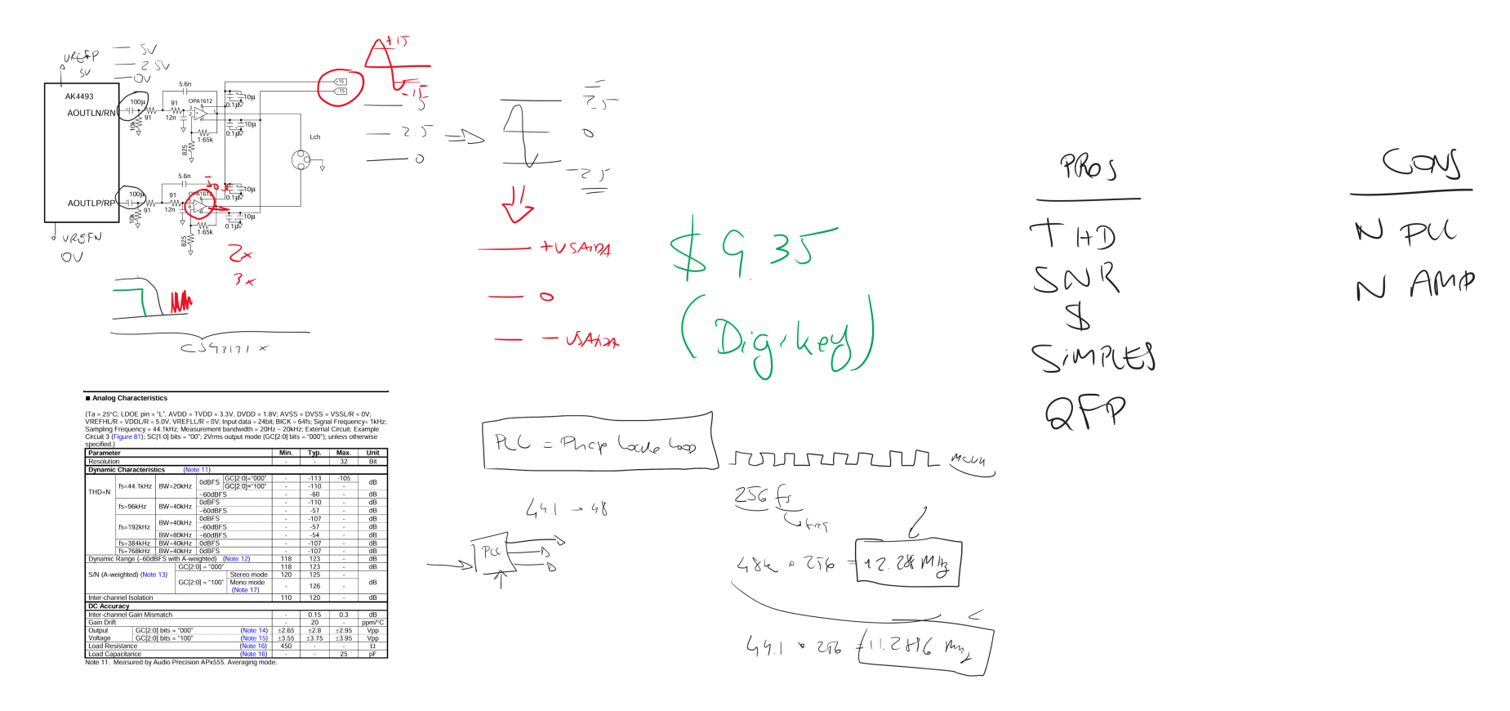
[picture p137: figure]

# Um resumo

Pros

SNR = 123dB

THD+N = -113dB

Barato

Design Simples

Programação Simples

Encapsulamento fácil

Cons

PLL externo

Amplificador externo

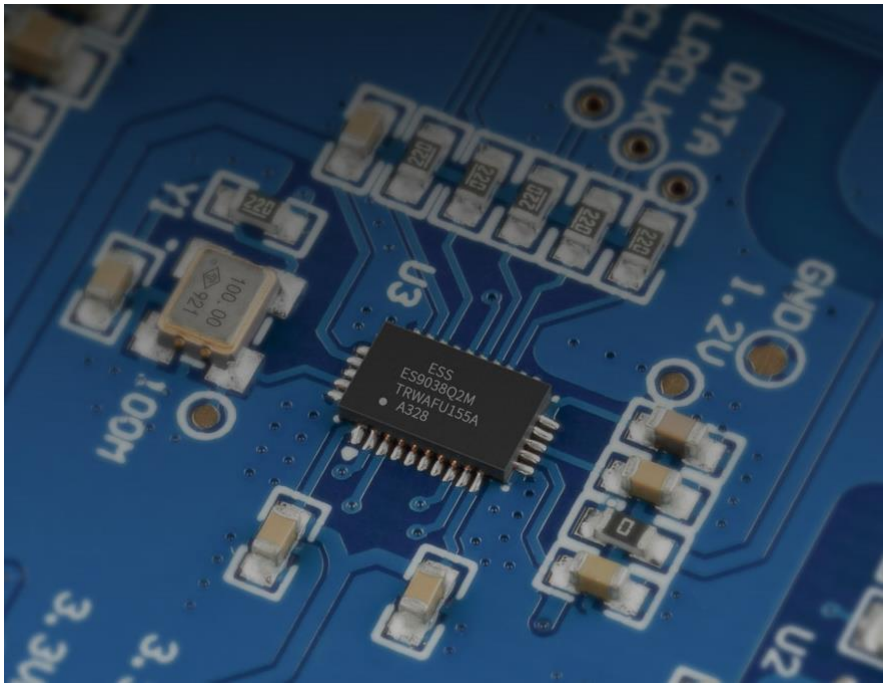
[picture p138: figure]

# Análise do ES9038Q2M
