yanava/mhd314/Simulations/ES9038 Out/es9038out.asc

C1: cap; 1.2n
C2: cap; 1.2n
C3: cap; 5.6n
C4: cap; 5.6n
C5: cap; 5.6n
C6: cap; 5.6n
C7: cap; 5.6n
C8: cap; 5.6n
I1: current; SINE(2.132m {Iac} 1000); AC 1
I2: current; SINE(2.132m {Iac} 1000 0 0 180); AC 1 180
R1: res; 1.21k
R2: res; 1.21k
R3: res; 681
R4: res; 232
R5: res; 681
R6: res; 232
R7: res; 25R
R8: res; 681
R9: res; 232
R10: res; 681
R11: res; 232
R12: res; 481
R13: res; 232
R14: res; 232
R15: res; 481
R16: res; 25R
U1: opamp2; OPA1611
U2: opamp2; OPA1622
U3: opamp2; OPA1622
U4: opamp2; OPA1622
U5: opamp2; OPA1611
V1: signal; 12V
V2: signal; 12V
Named nets: 0, VCC, VEE, plus, minus, se
.tran 0 10m 0 100n
.four 1k 20 10 V(plus,minus)
.include OPA1611.LIB
.options plotwinsize=0
.options numdgt=15
.param Iac=1.931m
.include OPA1622.LIB
