yanava/mhd314/Simulations/ES9038 Out/es9038OriginalOut.asc

C1: cap; 510p
C2: cap; 510p
C3: cap; 1n
C4: cap; 1n
I1: current; SINE(2.132m {Iac} 1000); AC 1
I2: current; SINE(2.132m {Iac} 1000 0 0 180); AC 1 180
R1: res; 2.37k
R2: res; 2.37k
R3: res; 10R
R4: res; 10R
R5: res; 300R
R6: res; 300R
R7: res; 200R
U1: opamp2; OPA1611
U5: opamp2; OPA1611
V1: signal; 12V
V2: signal; 12V
Named nets: 0, VCC, VEE, plus, minus
.tran 0 10m 0 1u
.four 1k 20 10 V(plus,minus)
.include OPA1611.LIB
.options plotwinsize=0
.options numdgt=15
.param Iac=1.931m
.include OPA1622.LIB
